Tekti/Ender3ProUpgrades/Y-axis tenstioner/Inside_+1mm.stl

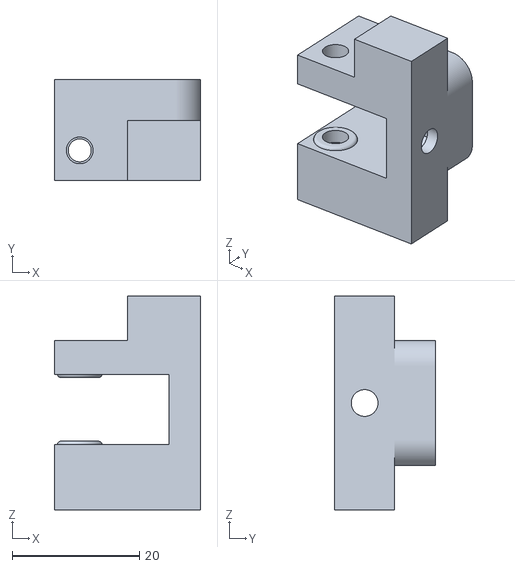
[picture p21: CAD file, 2021-11-08]
Y-axis tenstioner/Inside_+1mm.stl
23.0 x 15.8 x 33.6
