Tekti/Ender3ProUpgrades/Anti z-wobble squares/STLs/DirectDrive/Square_Middle.stl

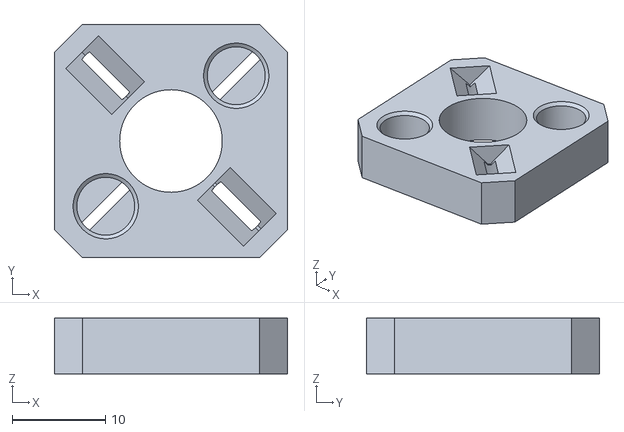
[picture p22: CAD file, 2021-05-25]
Anti z-wobble squares/STLs/DirectDrive/Square_Middle.stl
25.0 x 25.0 x 6.00
