Tekti/Ender3ProUpgrades/Anti z-wobble squares/STLs/DirectDrive_MetalPins/Heat inserts/Middle.3mf

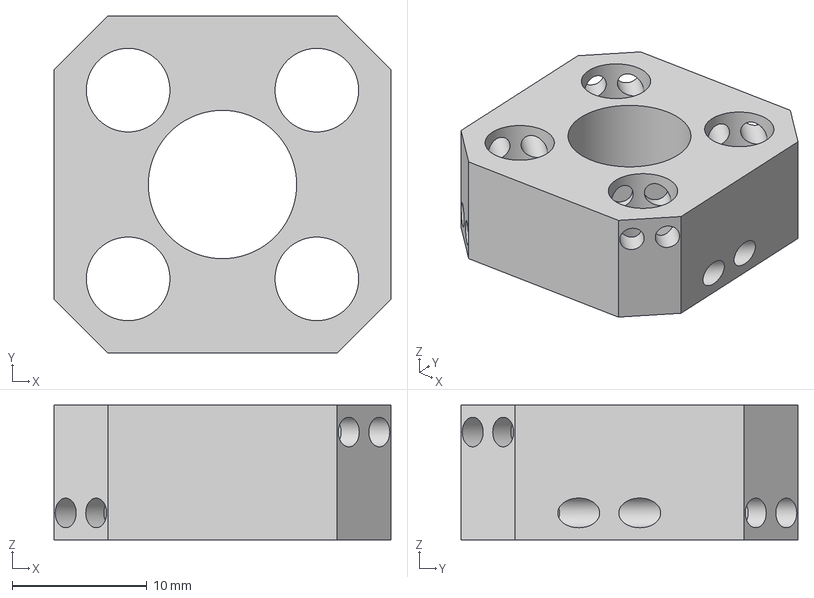
[picture p23: CAD file, 2021-10-25]
Anti z-wobble squares/STLs/DirectDrive_MetalPins/Heat inserts/Middle.3mf
25.0 x 25.0 x 10.0 mm
